thomasstar/GJ-Tho-Modular-V2/pictures/irlpic_turntable6.jpg

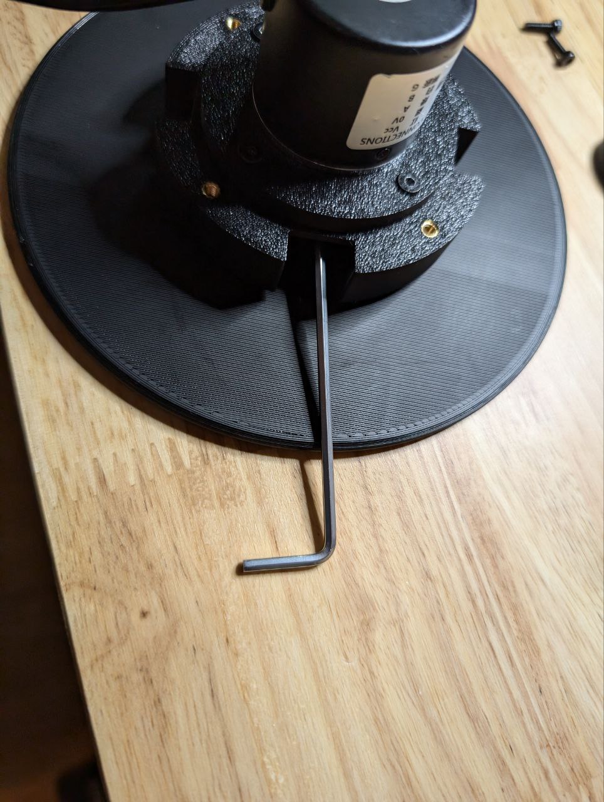
pictures/irlpic_turntable6.jpg
