thomasstar/GJ-Tho-Modular-V2/pictures/irlpic_turntable7.jpg

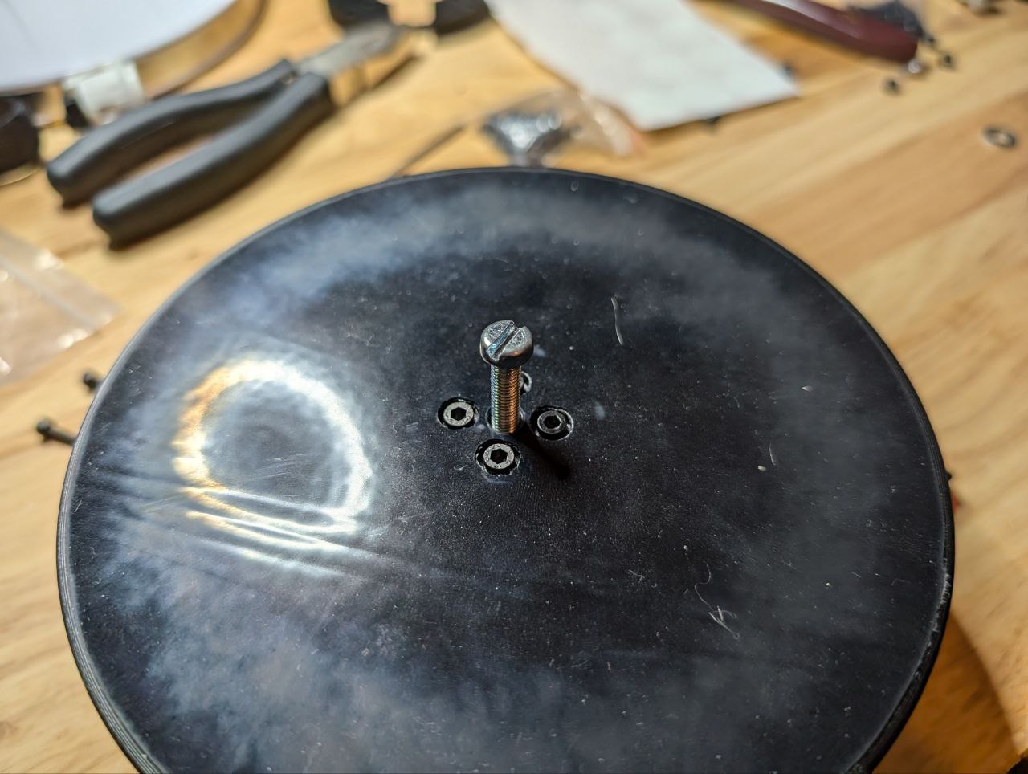
pictures/irlpic_turntable7.jpg
