thomasstar/GJ-Tho-Modular-V2/STL Turntable NEW/frame_center_shorter.stl

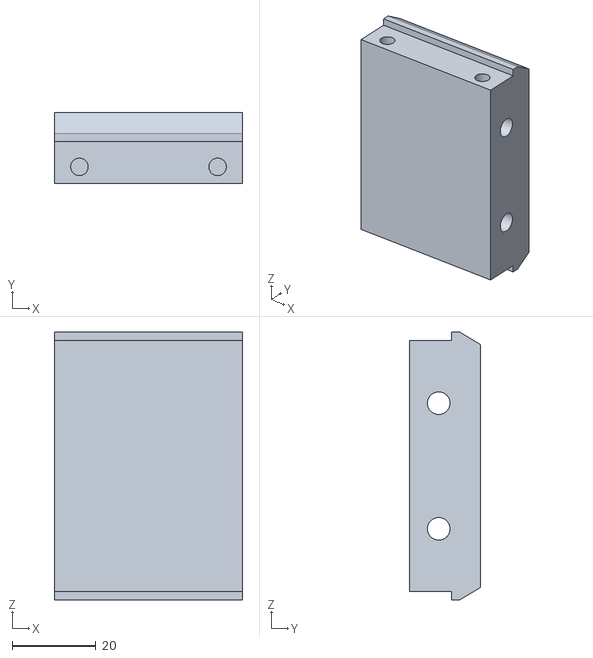
[picture p34: CAD file, 2025-02-06]
STL Turntable NEW/frame_center_shorter.stl
45.0 x 17.0 x 64.0
