thomasstar/GJ-Tho-Modular-V2/STL turntable/tt_spacer.stl

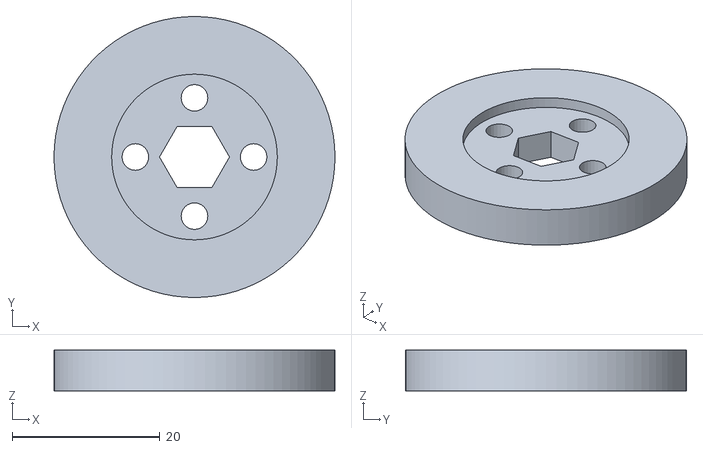
[picture p35: CAD file, 2024-09-14]
STL turntable/tt_spacer.stl
38.0 x 38.0 x 5.50
