thomasstar/GJ-Tho-Modular-V2/STL case/pcb-mount_pico.stl

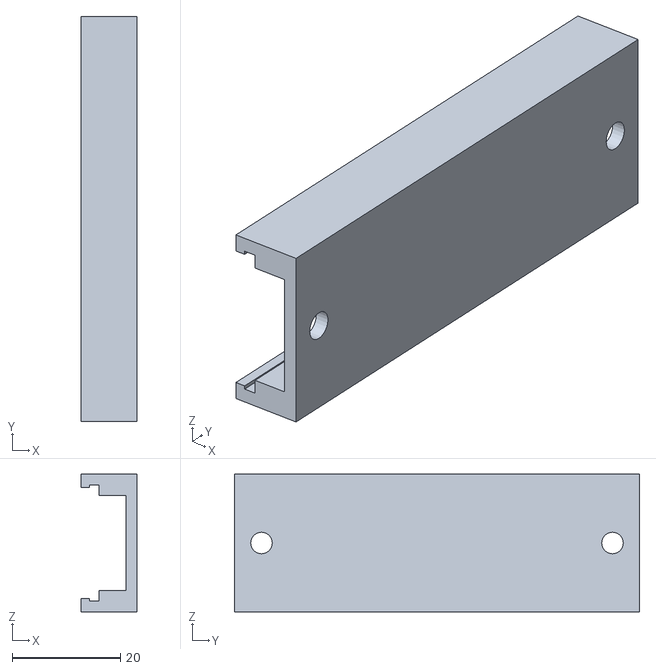
[picture p36: CAD file, 2024-09-14]
STL case/pcb-mount_pico.stl
10.3 x 75.0 x 25.5
