thomasstar/GJ-Tho-Modular-V2/STL Turntable NEW/tt_center.stl

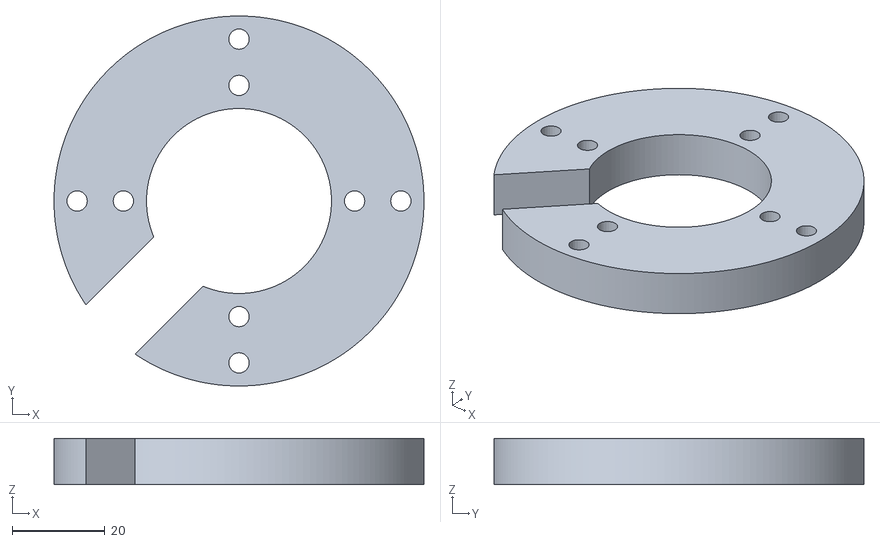
[picture p37: CAD file, 2025-02-05]
STL Turntable NEW/tt_center.stl
80.0 x 80.0 x 10.0
