thomasstar/GJ-Tho-Modular-V2/STL turntable/tt_cutguide.stl

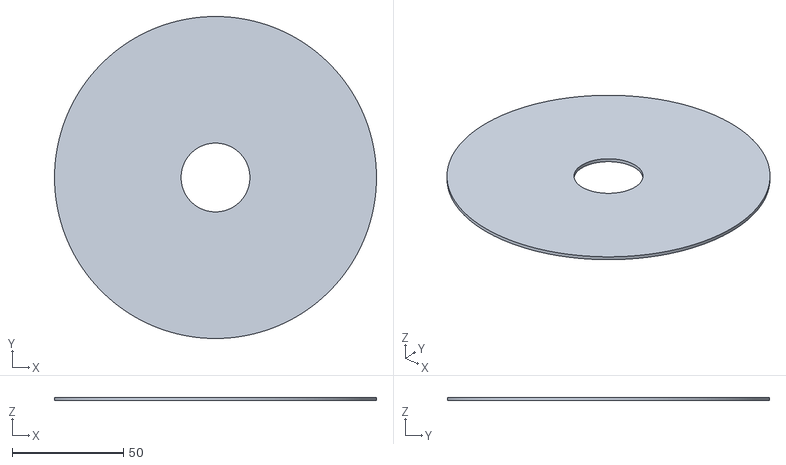
[picture p38: CAD file, 2024-09-14]
STL turntable/tt_cutguide.stl
145.0 x 145.0 x 1.50
