thomasstar/GJ-Tho-Modular-V2/STL Turntable NEW/tt_ledring.stl

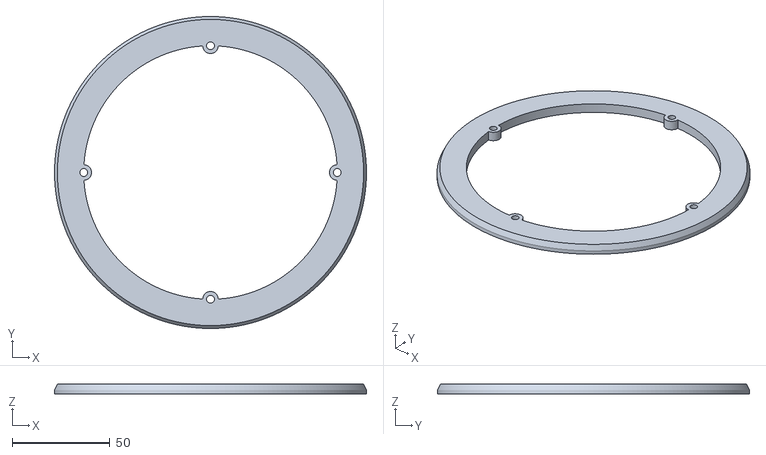
[picture p40: CAD file, 2025-02-05]
STL Turntable NEW/tt_ledring.stl
160.0 x 160.0 x 5.00
