thomasstar/GJ-Tho-Modular-V2/STL turntable/tt_lock.stl

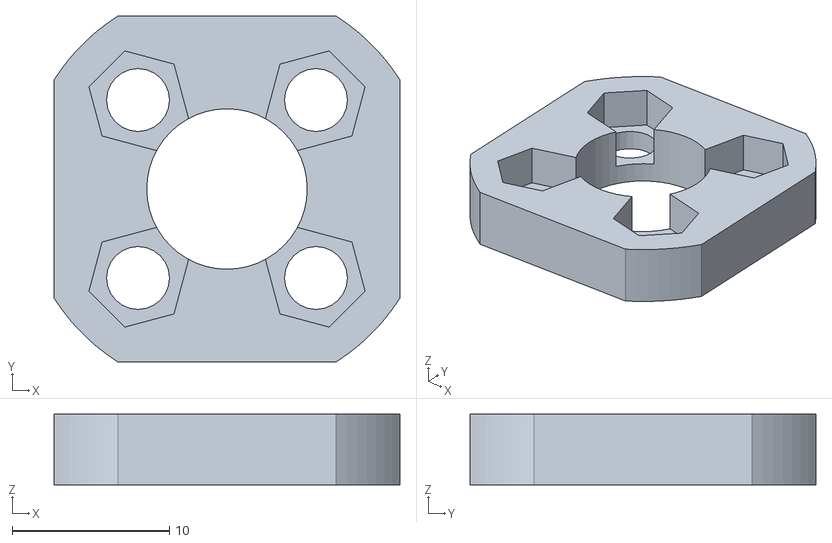
[picture p41: CAD file, 2024-09-14]
STL turntable/tt_lock.stl
22.0 x 22.0 x 4.50
