thomasstar/GJ-Tho-Modular-V2/STL case/frame_a.stl

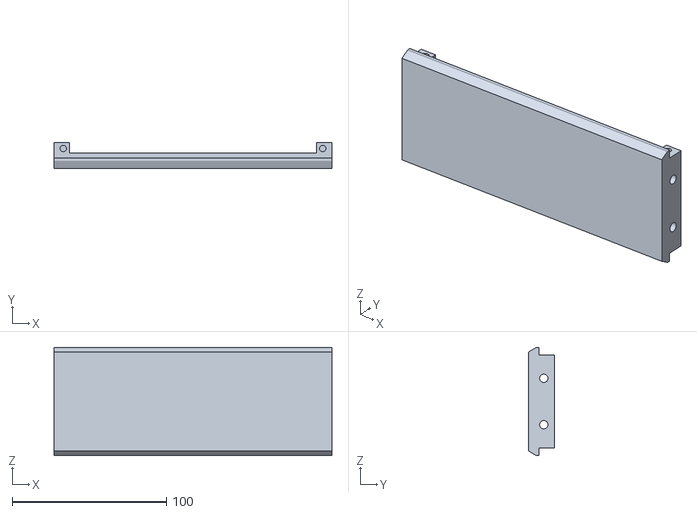
[picture p42: CAD file, 2024-09-14]
STL case/frame_a.stl
180.0 x 17.0 x 70.0
