thomasstar/GJ-Tho-Modular-V2/STL Turntable NEW/tt_top.stl

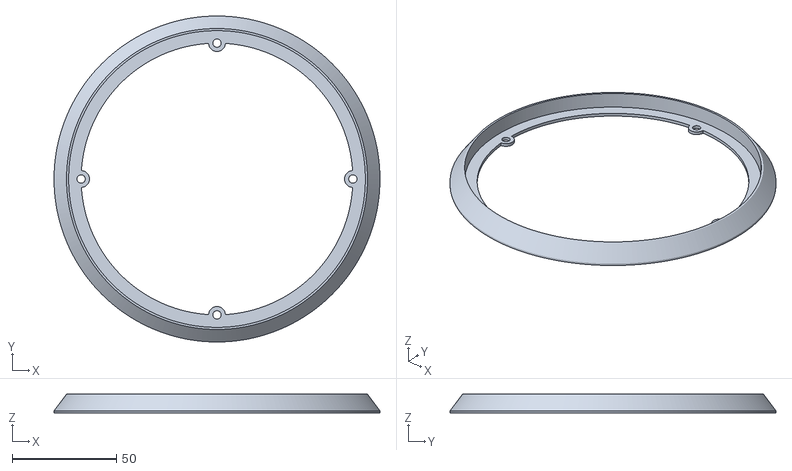
[picture p43: CAD file, 2025-02-05]
STL Turntable NEW/tt_top.stl
156.0 x 156.0 x 9.00
