thomasstar/GJ-Tho-Modular-V2/STL turntable/tt_disc.stl

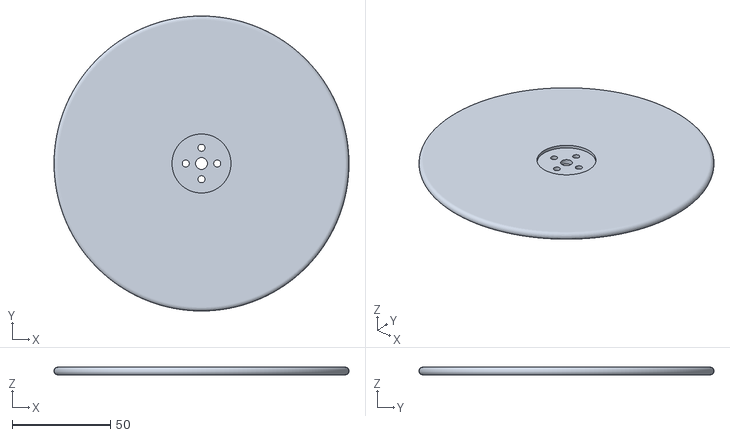
[picture p44: CAD file, 2024-09-14]
STL turntable/tt_disc.stl
150.0 x 150.0 x 4.00
