thomasstar/GJ-Tho-Modular-V2/STL Turntable NEW/tt_ledcover.stl

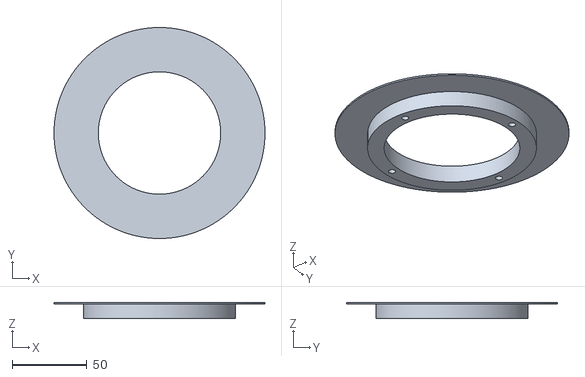
[picture p45: CAD file, 2025-02-05]
STL Turntable NEW/tt_ledcover.stl
141.4 x 141.4 x 11.0
