thomasstar/GJ-Tho-Modular-V2/STL case/panel_buttons_4e.stl

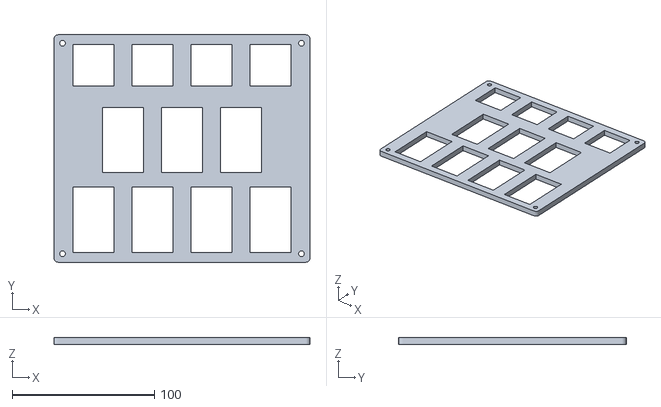
[picture p46: CAD file, 2024-09-14]
STL case/panel_buttons_4e.stl
180.0 x 160.0 x 5.00
