thomasstar/GJ-Tho-Modular-V2/STL case/side_usb.stl

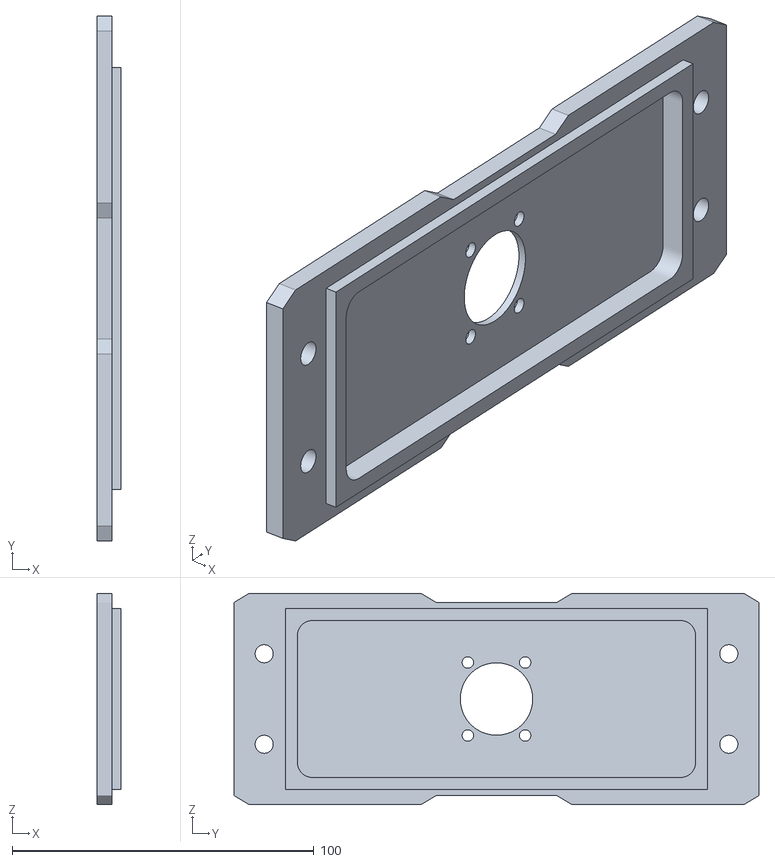
[picture p47: CAD file, 2024-09-14]
STL case/side_usb.stl
8.00 x 174.0 x 70.0
