thomasstar/GJ-Tho-Modular-V2/STL case/panel_center.stl

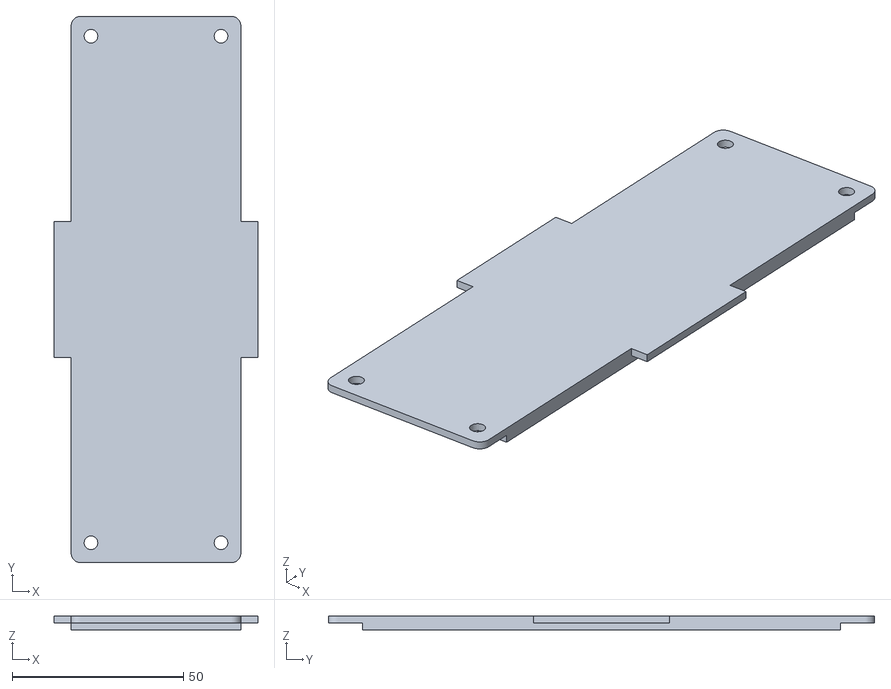
[picture p48: CAD file, 2024-09-14]
STL case/panel_center.stl
59.6 x 159.6 x 4.00
