thomasstar/GJ-Tho-Modular-V2/STL case/side.stl

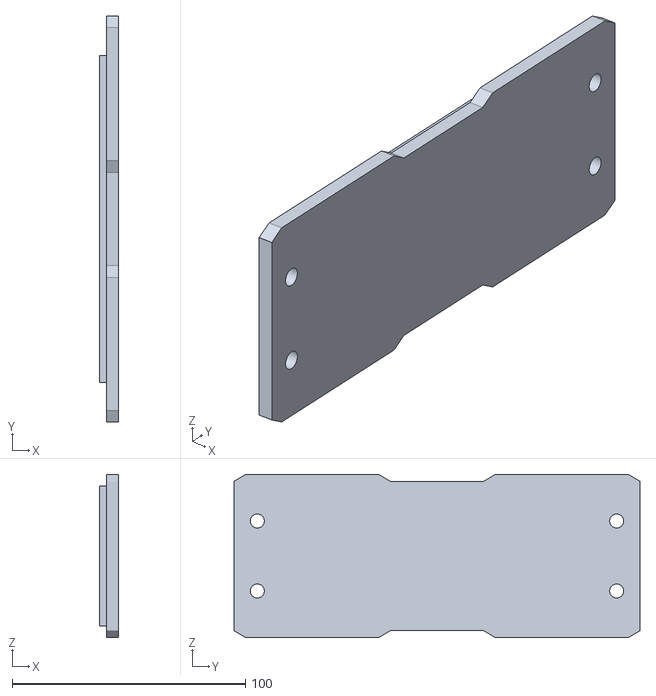
[picture p49: CAD file, 2024-09-14]
STL case/side.stl
8.00 x 174.0 x 70.0
